TeodorStamatin/EBook_Reader/Images/Display.png

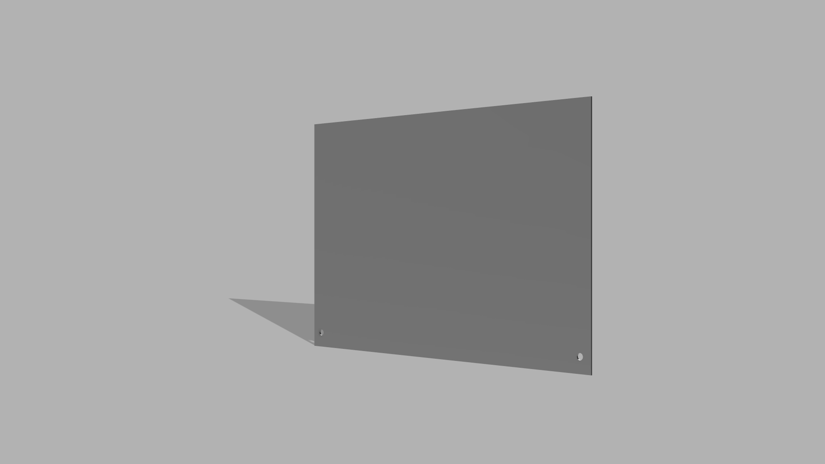
Images/Display.png
