TeodorStamatin/EBook_Reader/Images/OpenBookReader_exploded2.png

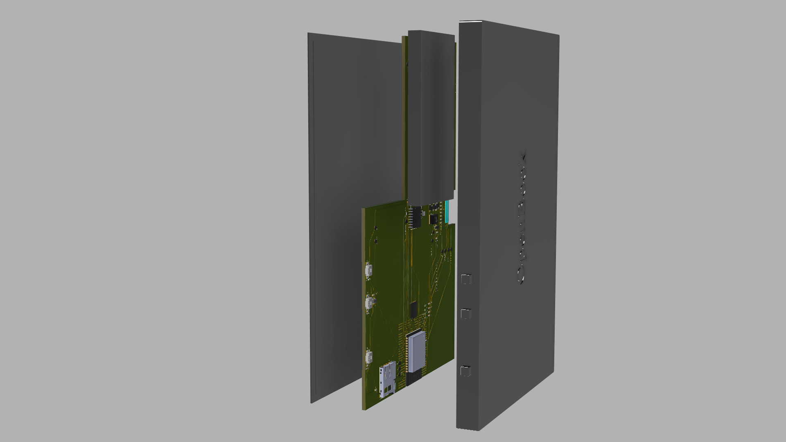
Images/OpenBookReader_exploded2.png
