TeodorStamatin/EBook_Reader/Images/OpenBookReader_SideProfile.png

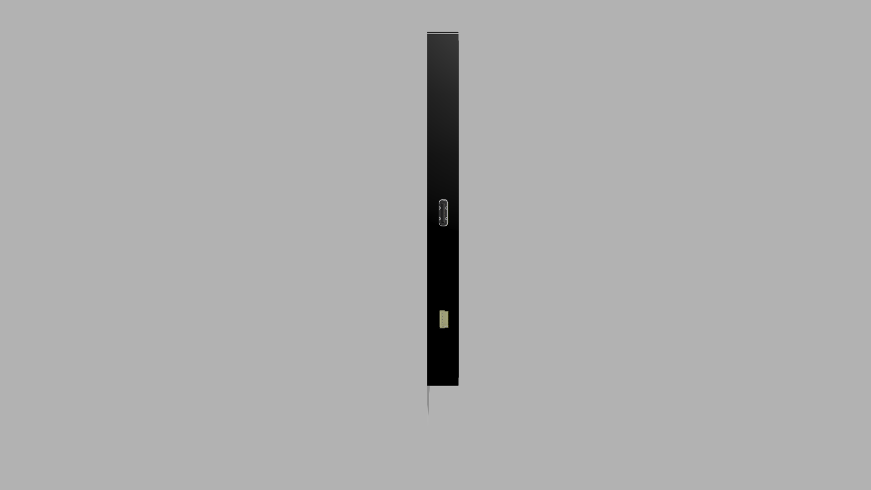
Images/OpenBookReader_SideProfile.png
